samuelclay/turntouch-enclosure/inventor/STLs/Remote Assembly_Remote Top_1.stl

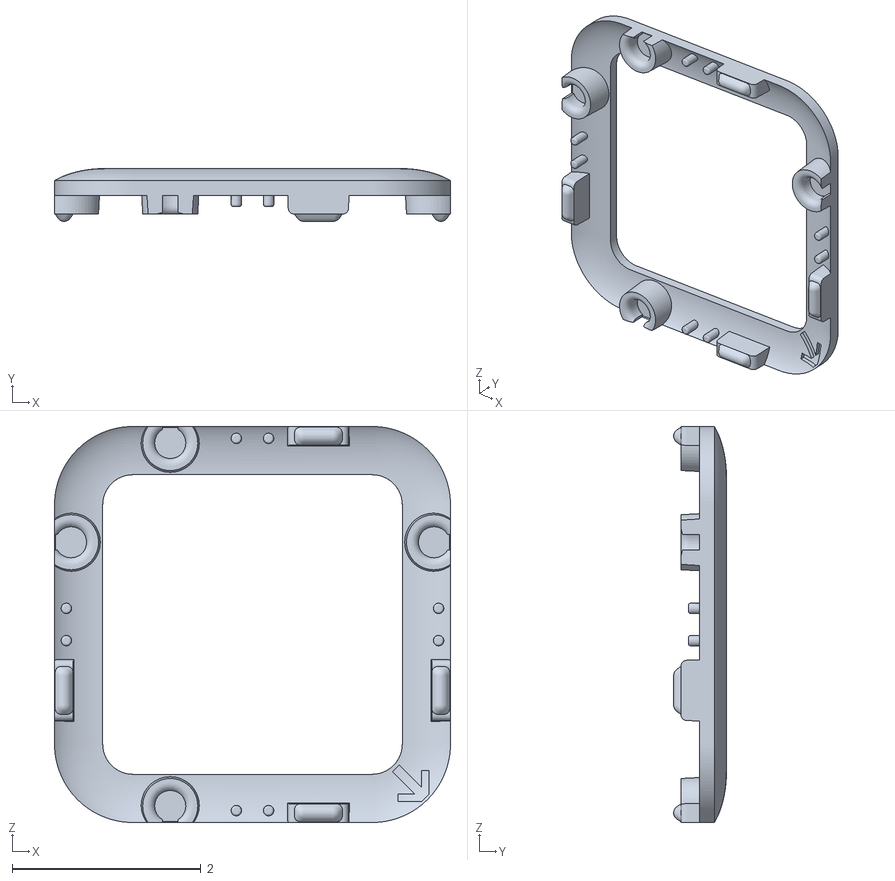
[picture p15: CAD file, 2016-02-05]
inventor/STLs/Remote Assembly_Remote Top_1.stl
4.20 x 0.56 x 4.20
