samuelclay/turntouch-enclosure/revisions/Turn Touch Remote Rev. 29/Remote Assembly_Eagle PCB rev 21_7.stl

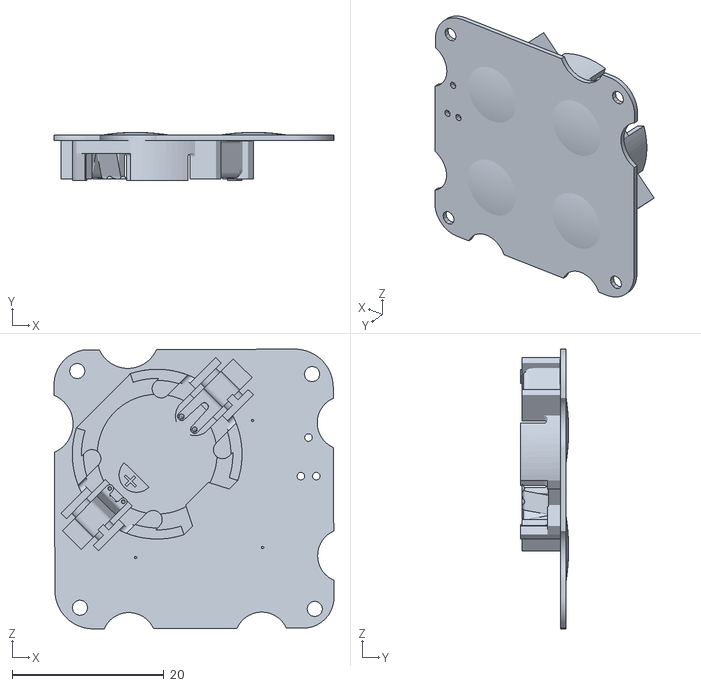
[picture p16: CAD file, 2015-10-15]
revisions/Turn Touch Remote Rev. 29/Remote Assembly_Eagle PCB rev 21_7.stl
37.0 x 6.37 x 36.9
