samuelclay/turntouch-enclosure/inventor/STLs/Remote Assembly_Remote Bottom_3.stl

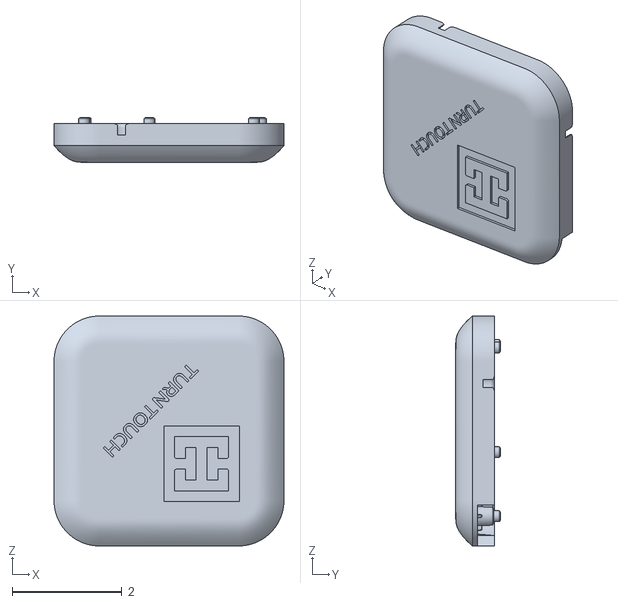
[picture p17: CAD file, 2016-02-05]
inventor/STLs/Remote Assembly_Remote Bottom_3.stl
4.20 x 0.813 x 4.20
