samuelclay/turntouch-enclosure/revisions/Turn Touch Remote Rev. 29/Remote Assembly_Remote Bottom_3.stl

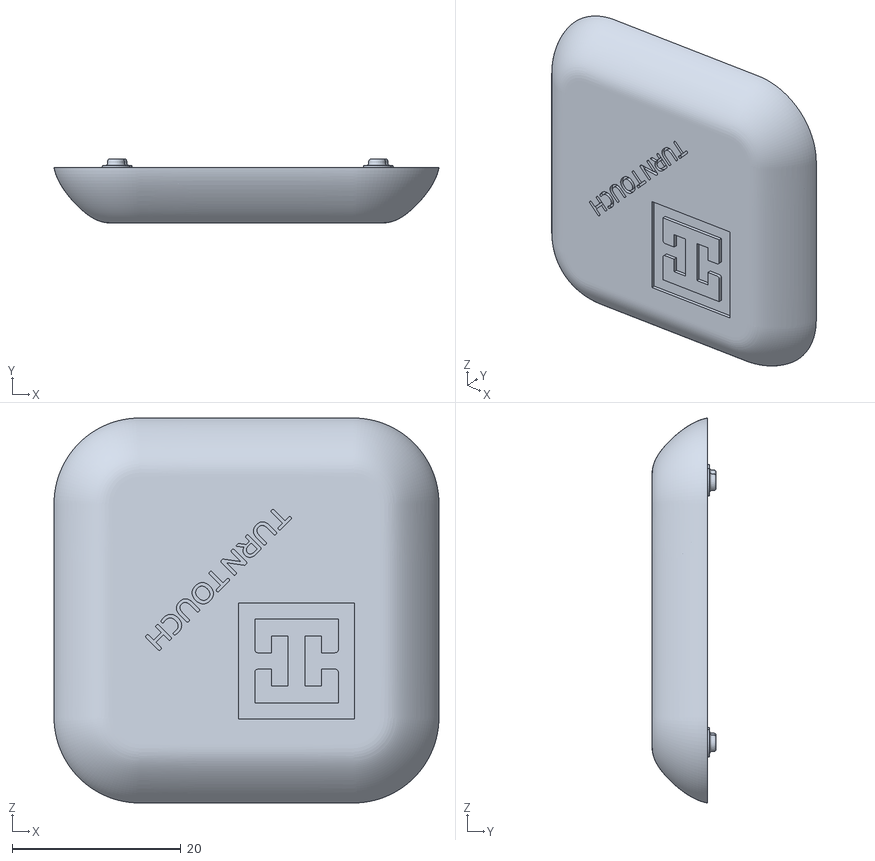
[picture p18: CAD file, 2015-10-15]
revisions/Turn Touch Remote Rev. 29/Remote Assembly_Remote Bottom_3.stl
45.7 x 7.62 x 45.7
