samuelclay/turntouch-enclosure/buttons.stl

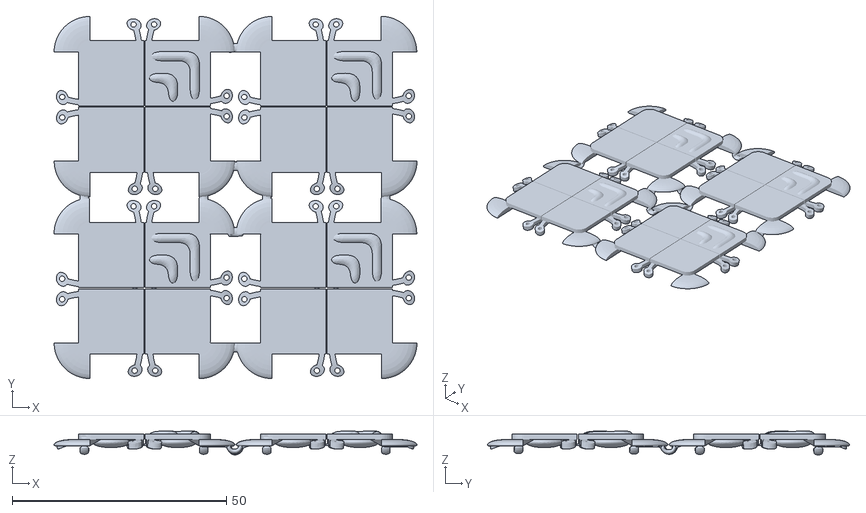
[picture p19: CAD file, 2015-05-16]
buttons.stl
84.7 x 84.5 x 5.56
