samuelclay/turntouch-enclosure/inventor/STLs/Magnet Top Insertion Jig.stl

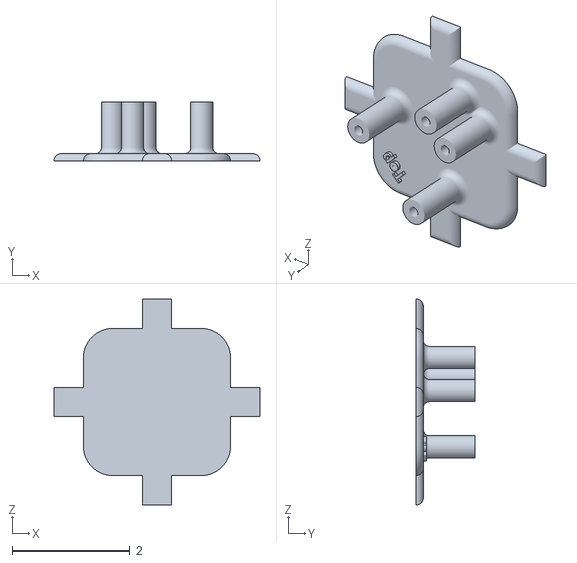
[picture p20: CAD file, 2017-12-07]
inventor/STLs/Magnet Top Insertion Jig.stl
3.50 x 1.00 x 3.50
