samuelclay/turntouch-enclosure/revisions/Turn Touch Remote IGES rev 29/Remote Buttons.igs

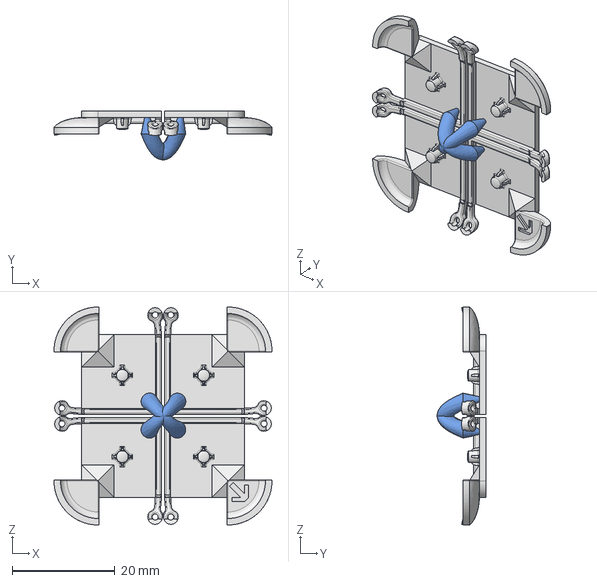
[picture p21: CAD file, 2015-10-19]
revisions/Turn Touch Remote IGES rev 29/Remote Buttons.igs
42.5 x 9.52 x 42.5 mm
