samuelclay/turntouch-enclosure/revisions/Turn Touch Remote rev 31/Plastic Remote Top.stp

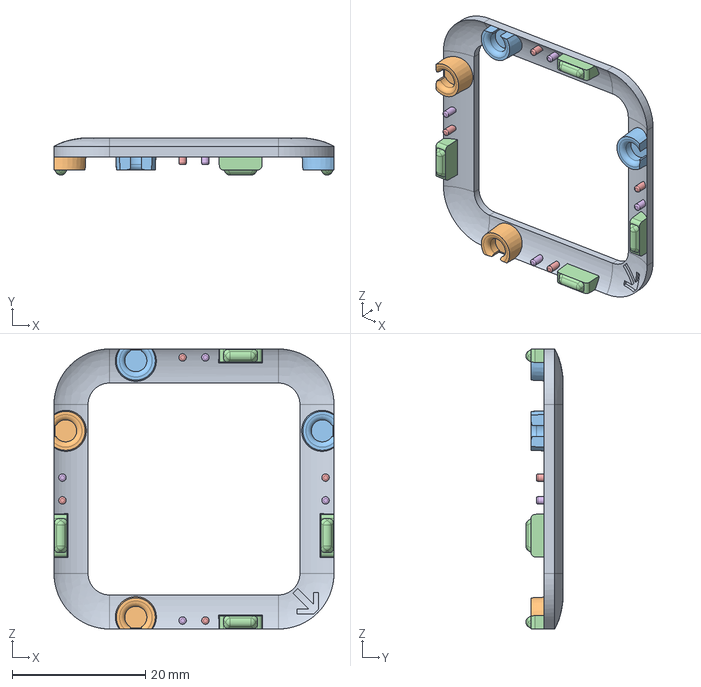
[picture p22: CAD file, 2016-02-05]
revisions/Turn Touch Remote rev 31/Plastic Remote Top.stp
42.0 x 5.60 x 42.0 mm
