samuelclay/turntouch-enclosure/revisions/Turn Touch rev 39/Remote Top.stp

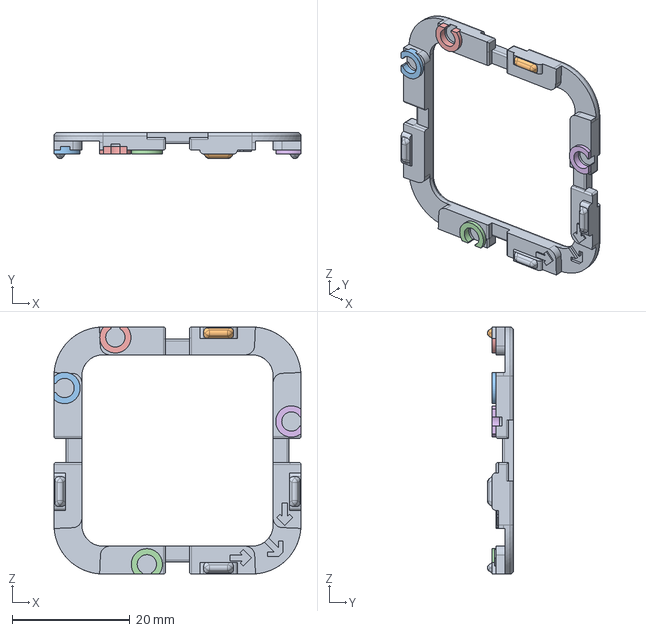
[picture p23: CAD file, 2017-05-08]
revisions/Turn Touch rev 39/Remote Top.stp
42.0 x 4.48 x 42.0 mm
