samuelclay/turntouch-enclosure/rhino/bottoms.stp

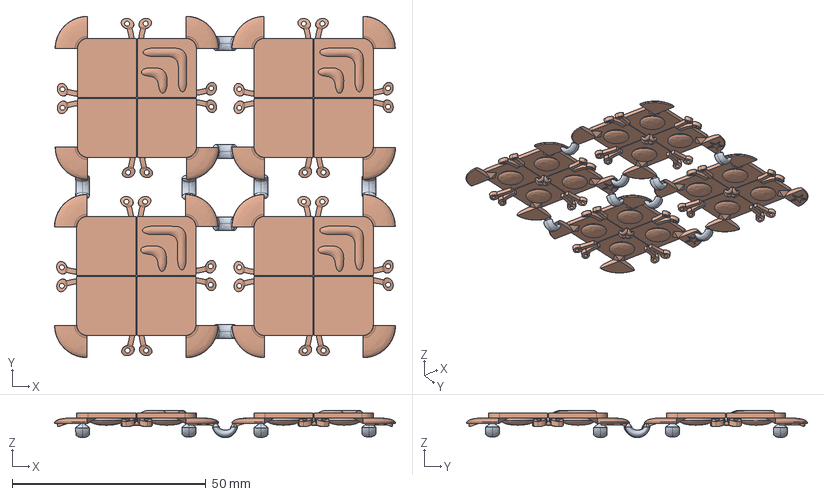
[picture p24: CAD file, 2015-06-04]
rhino/bottoms.stp
87.9 x 88.0 x 7.06 mm
