samuelclay/turntouch-enclosure/solidworks/Remote Buttons.SLDPRT

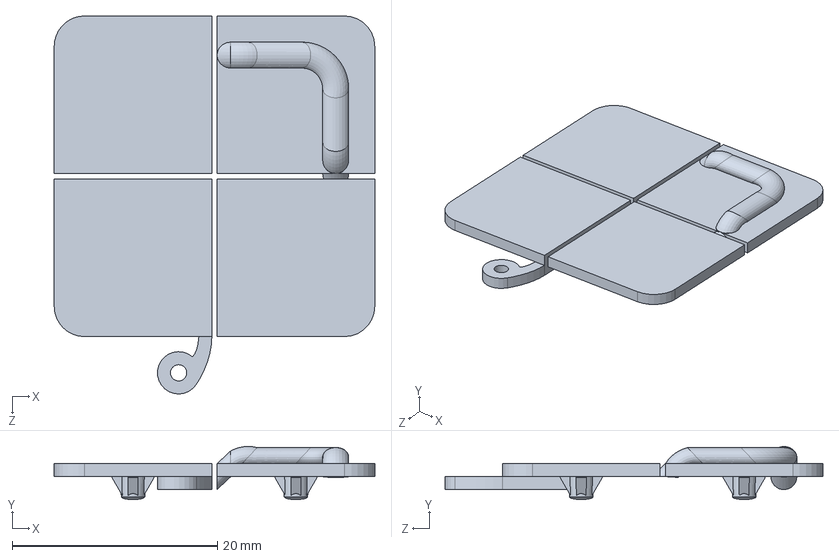
[picture p25: CAD file, 2015-06-16]
solidworks/Remote Buttons.SLDPRT
31.2 x 5.17 x 36.8 mm
