samuelclay/turntouch-enclosure/revisions/Turn Touch Remote IGES rev 29/Case Bottom.igs

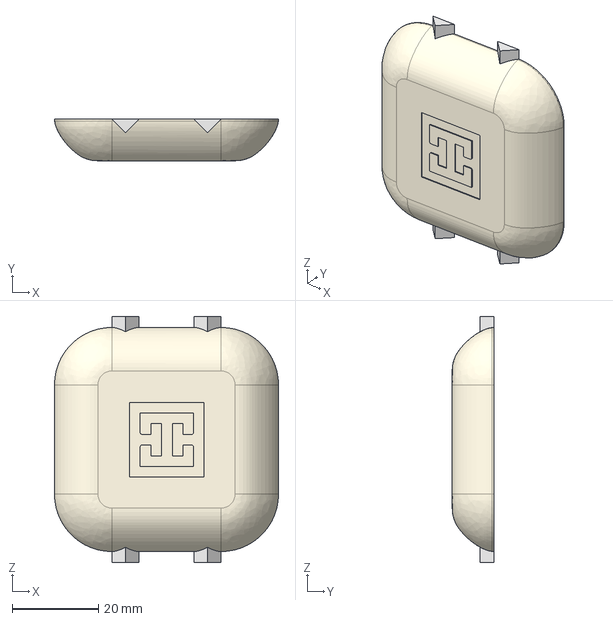
[picture p26: CAD file, 2015-10-19]
revisions/Turn Touch Remote IGES rev 29/Case Bottom.igs
51.9 x 9.63 x 57.0 mm
