samuelclay/turntouch-enclosure/revisions/Turn Touch rev 39/Remote Bottom.stp

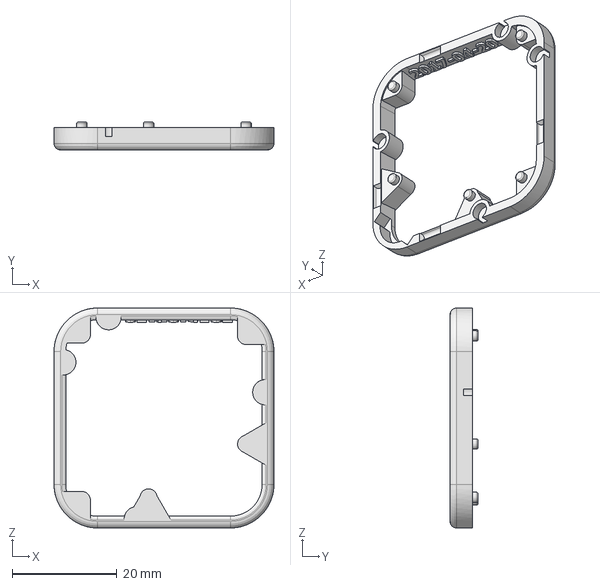
[picture p27: CAD file, 2017-05-08]
revisions/Turn Touch rev 39/Remote Bottom.stp
42.0 x 5.33 x 42.0 mm
