samuelclay/turntouch-enclosure/tops.stl

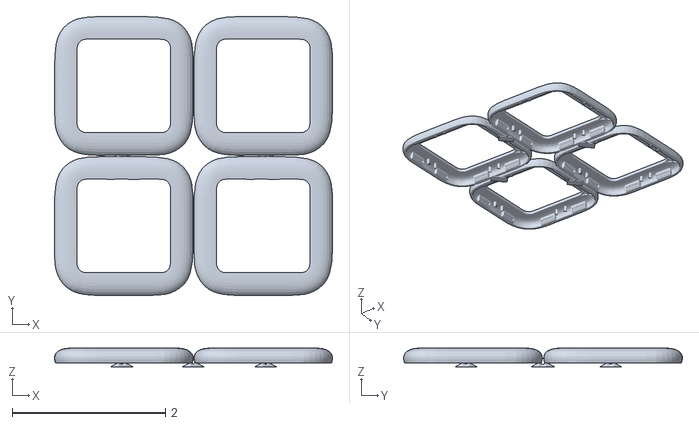
[picture p28: CAD file, 2015-05-07]
tops.stl
3.63 x 3.64 x 0.246
