samuelclay/turntouch-enclosure/bottoms.stl

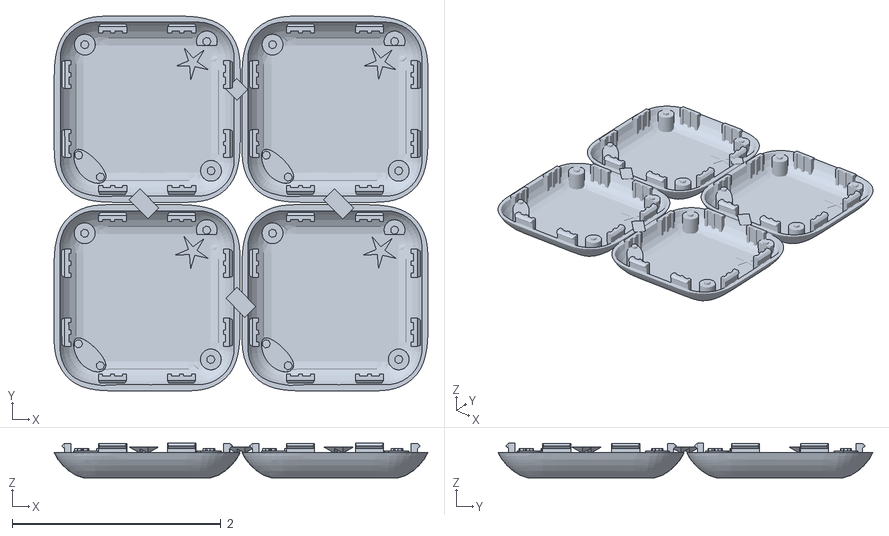
[picture p29: CAD file, 2015-05-07]
bottoms.stl
3.59 x 3.60 x 0.331
