samuelclay/turntouch-enclosure/inventor/STLs/Build Button Top Jig.stl

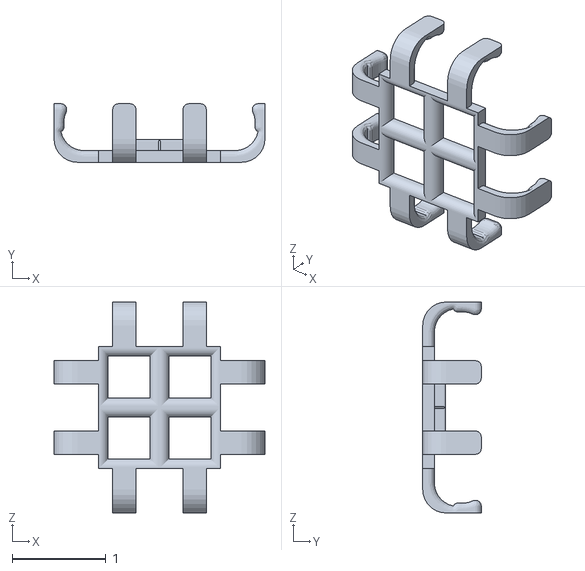
[picture p30: CAD file, 2017-12-01]
inventor/STLs/Build Button Top Jig.stl
2.25 x 0.625 x 2.25
