samuelclay/turntouch-enclosure/revisions/Turn Touch Remote IGES rev 29/Case Buttons.igs

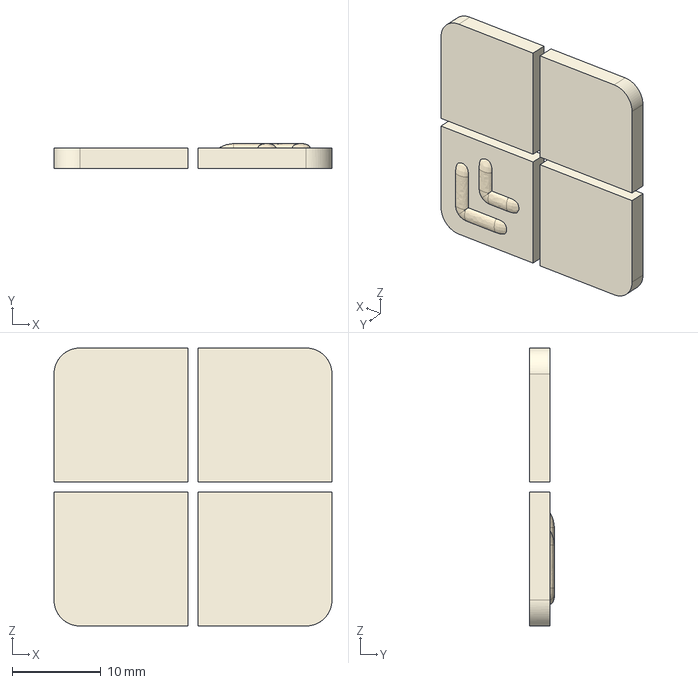
[picture p31: CAD file, 2015-10-19]
revisions/Turn Touch Remote IGES rev 29/Case Buttons.igs
31.2 x 2.79 x 31.2 mm
