samuelclay/turntouch-enclosure/revisions/Turn Touch Remote rev 31/Wood Case Bottom.stp

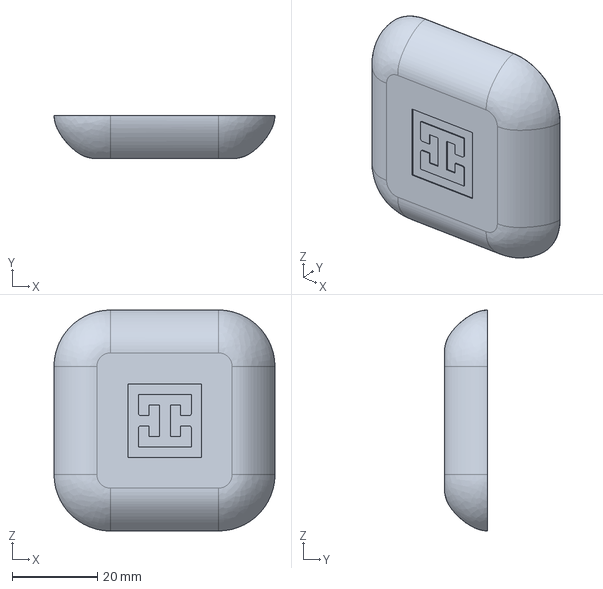
[picture p32: CAD file, 2016-02-05]
revisions/Turn Touch Remote rev 31/Wood Case Bottom.stp
51.9 x 10.2 x 51.9 mm
