samuelclay/turntouch-enclosure/revisions/Turn Touch rev 39/Remote Buttons.stp

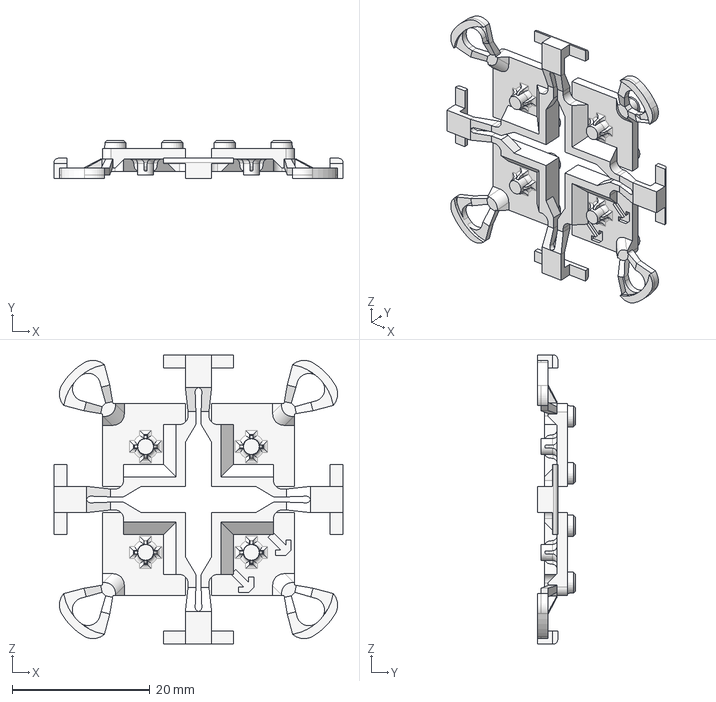
[picture p33: CAD file, 2017-05-08]
revisions/Turn Touch rev 39/Remote Buttons.stp
42.0 x 5.47 x 42.0 mm
