samuelclay/turntouch-enclosure/rhino/tops.stp

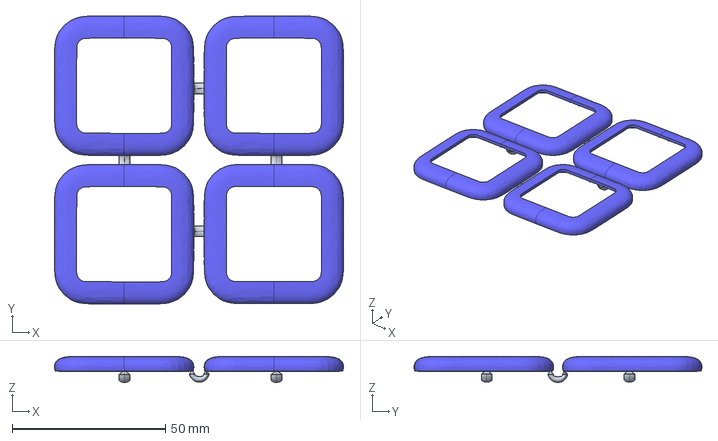
[picture p34: CAD file, 2015-05-22]
rhino/tops.stp
94.2 x 93.9 x 8.49 mm
