samuelclay/turntouch-enclosure/solidworks/Remote Top.sldprt

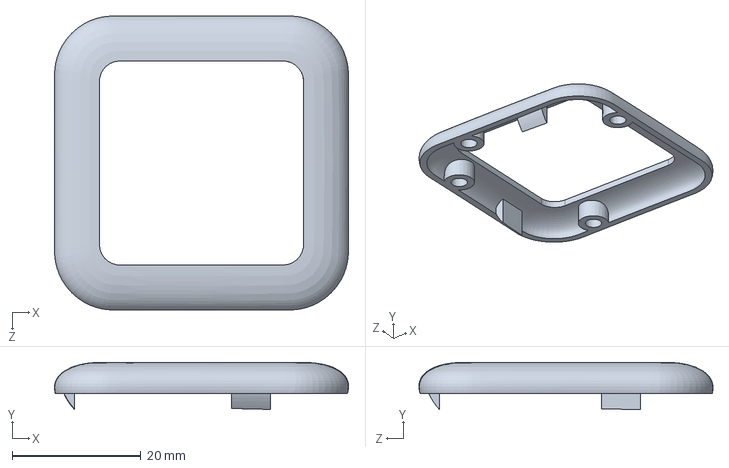
[picture p35: CAD file, 2015-06-13]
solidworks/Remote Top.sldprt
45.7 x 7.36 x 45.7 mm
