samuelclay/turntouch-enclosure/inventor/STEPs/Under Case Button Booster.stp

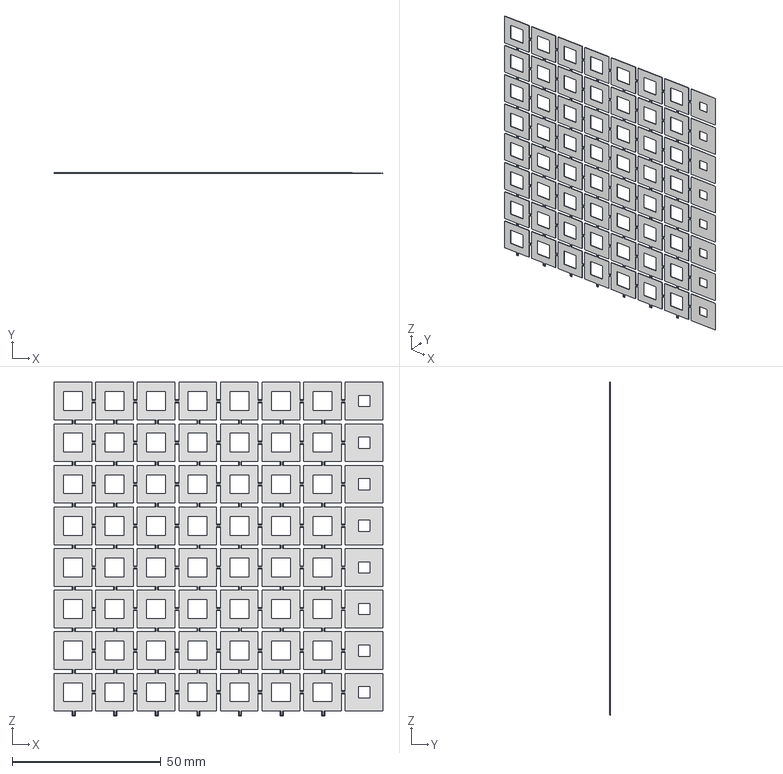
[picture p36: CAD file, 2016-10-12]
inventor/STEPs/Under Case Button Booster.stp
110.5 x 0.254 x 112.1 mm
