samuelclay/turntouch-enclosure/inventor/STLs/Under Case Photo Holder.stl

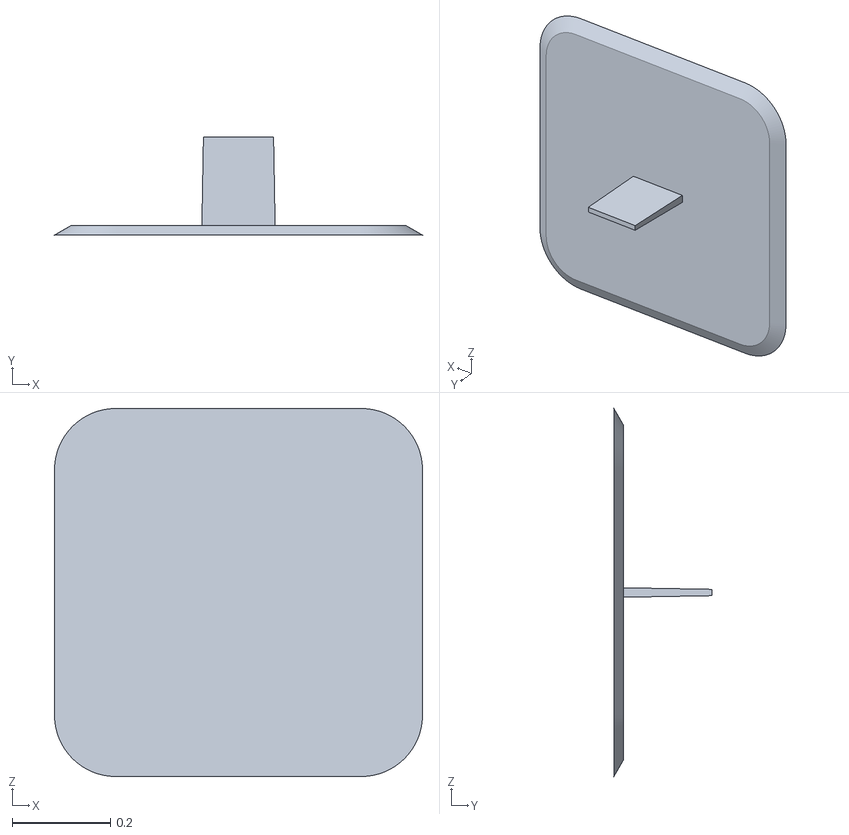
[picture p37: CAD file, 2017-01-26]
inventor/STLs/Under Case Photo Holder.stl
0.75 x 0.2 x 0.75
