samuelclay/turntouch-enclosure/Remote enclosure.obj

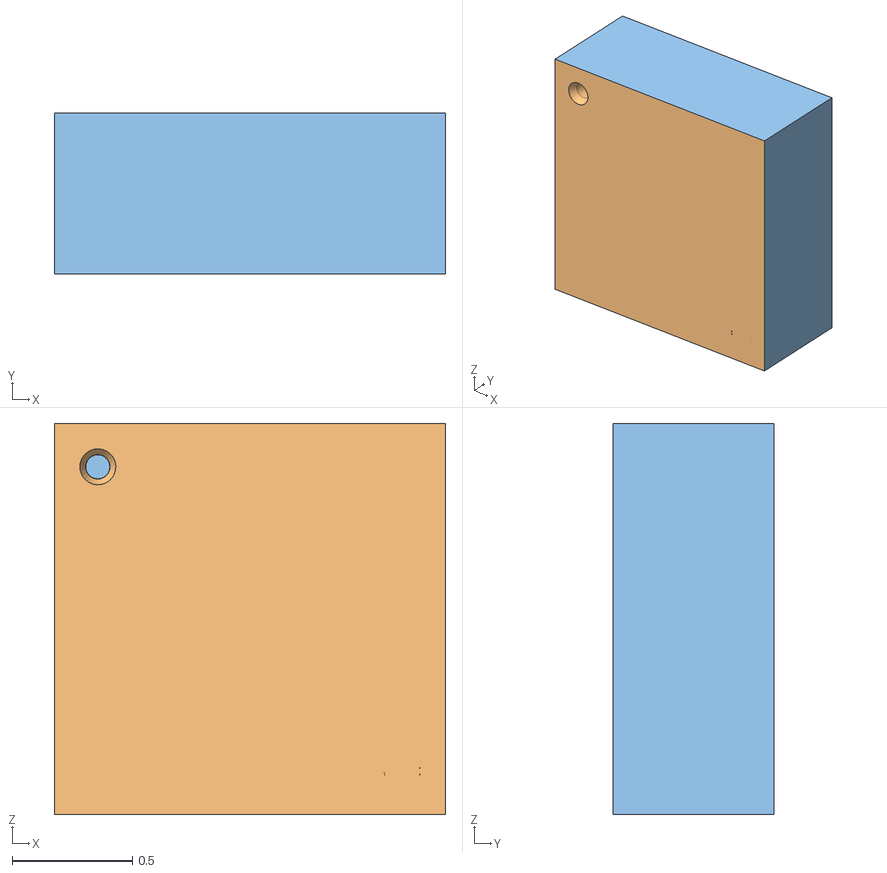
[picture p38: CAD file, 2014-10-08]
Remote enclosure.obj
1.63 x 0.67 x 1.62
Mesh1 PCB Model
Mesh91 Bottom___05__walls_ Model
Mesh102 Top___05__walls_ Model
Mesh116 Button_cap1 Model
Mesh120 Button_cap2 Model
Mesh124 Button_cap3 Model
Mesh128 Button_cap4 Model
