samuelclay/turntouch-enclosure/revisions/Turn Touch Remote rev 31/Wood Case Top.stp

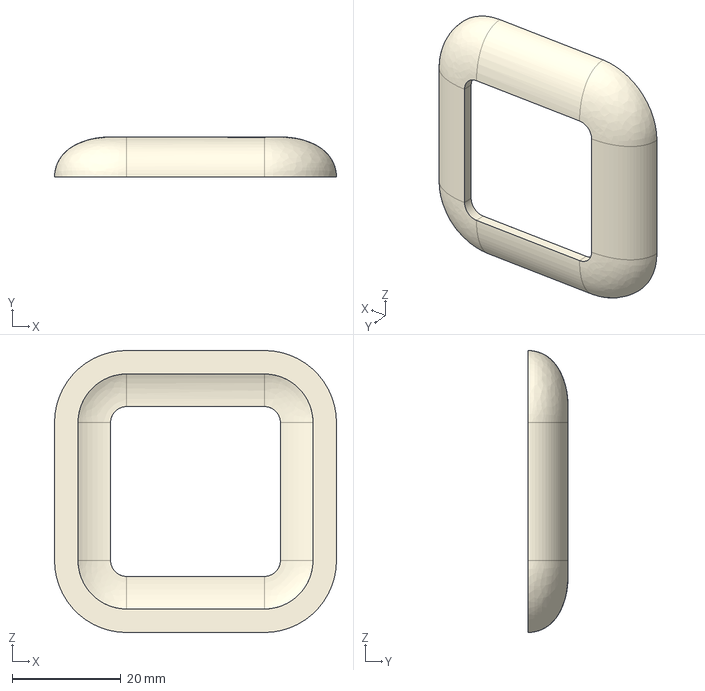
[picture p39: CAD file, 2016-02-05]
revisions/Turn Touch Remote rev 31/Wood Case Top.stp
51.9 x 7.37 x 51.9 mm
