samuelclay/turntouch-enclosure/rhino/remote.stp

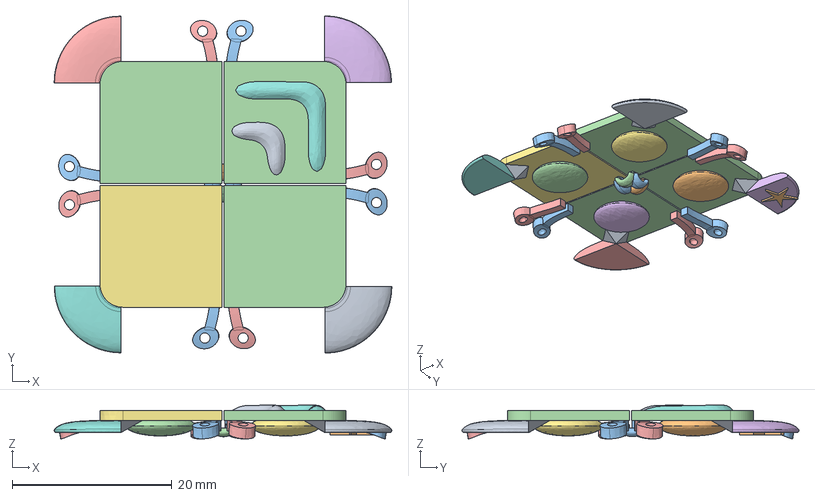
[picture p40: CAD file, 2015-05-19]
rhino/remote.stp
42.2 x 42.1 x 4.23 mm
