samuelclay/turntouch-enclosure/solidworks/PCB.SLDPRT

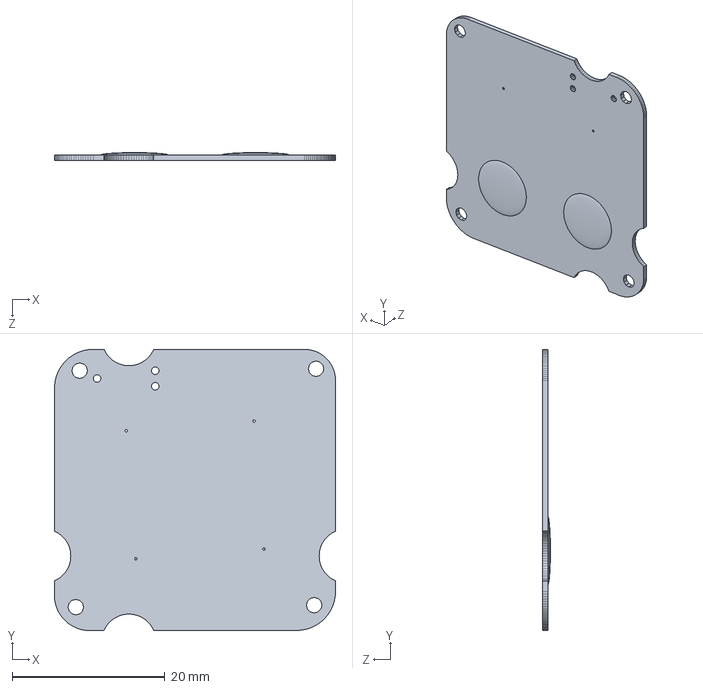
[picture p41: CAD file, 2015-06-09]
solidworks/PCB.SLDPRT
36.8 x 36.9 x 1.03 mm
