samuelclay/turntouch-enclosure/inventor/Eagle PCB rev 38.dxf

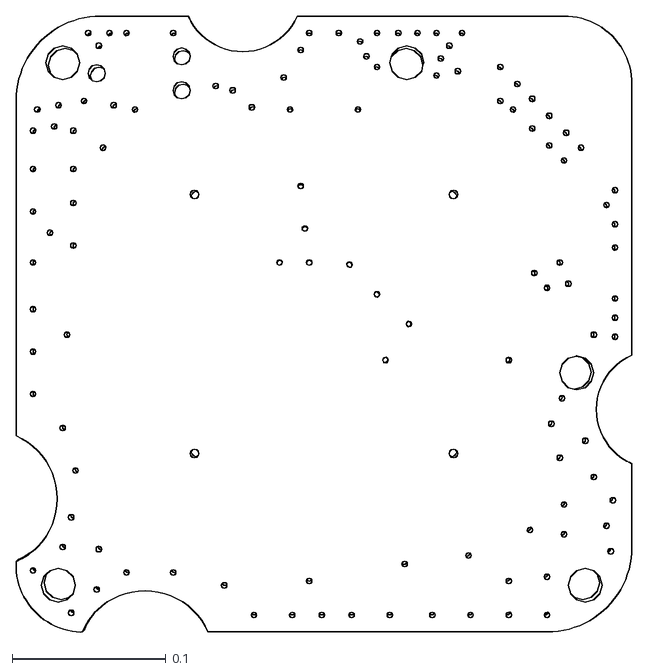
[picture p42: CAD file, 2017-04-11]
inventor/Eagle PCB rev 38.dxf
0.4 x 0.4
