samuelclay/turntouch-enclosure/revisions/Turn Touch Remote rev 31/Plastic Remote Bottom.stp

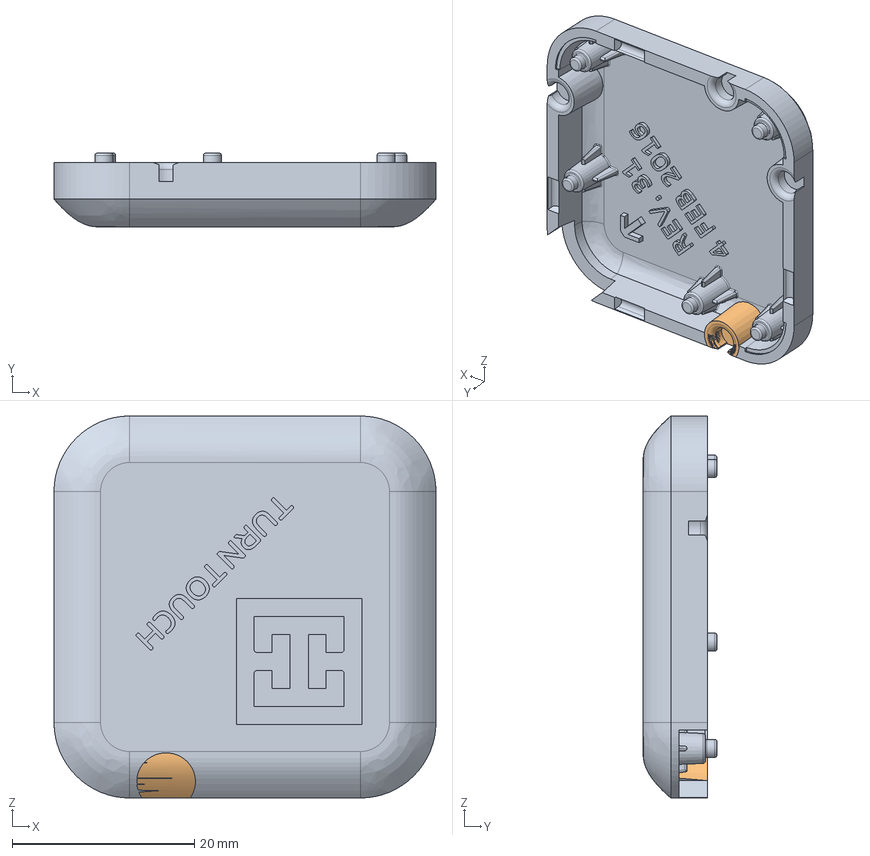
[picture p43: CAD file, 2016-02-05]
revisions/Turn Touch Remote rev 31/Plastic Remote Bottom.stp
42.0 x 8.13 x 42.0 mm
