samuelclay/turntouch-enclosure/solidworks/Remote Bottom.sldprt

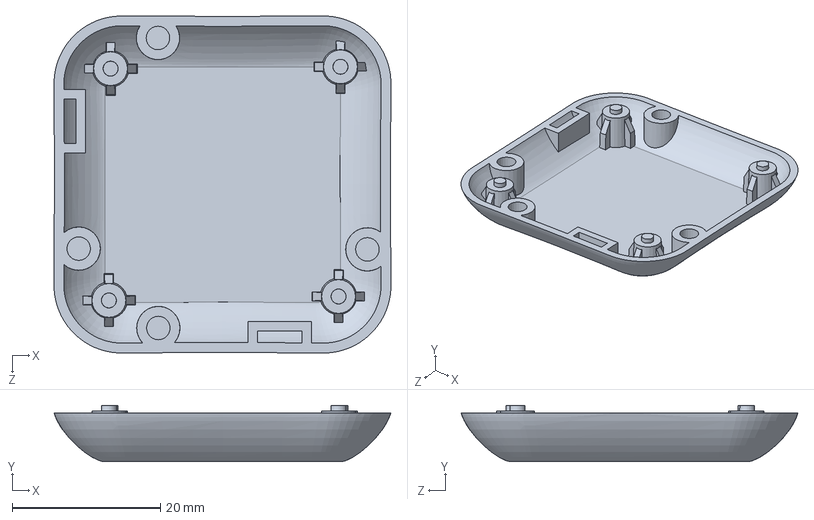
[picture p44: CAD file, 2015-06-07]
solidworks/Remote Bottom.sldprt
45.5 x 7.62 x 45.5 mm
