samuelclay/turntouch-enclosure/revisions/Turn Touch Remote IGES rev 29/Case Top.igs

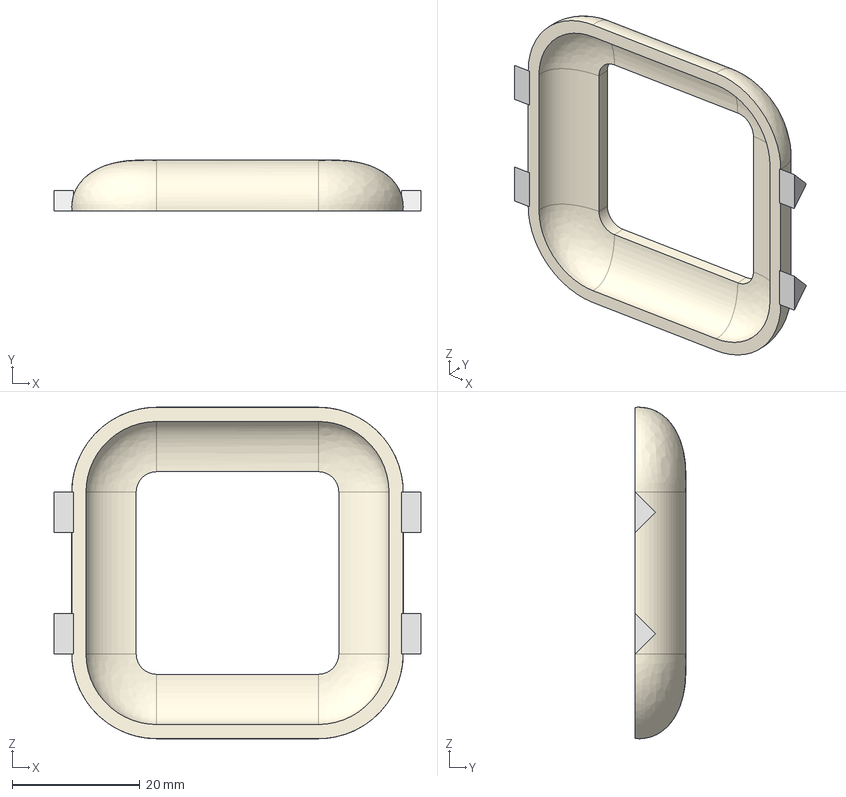
[picture p45: CAD file, 2015-10-19]
revisions/Turn Touch Remote IGES rev 29/Case Top.igs
57.5 x 7.92 x 52.0 mm
