samuelclay/turntouch-enclosure/revisions/Turn Touch Remote rev 31/Wood Case Buttons.stp

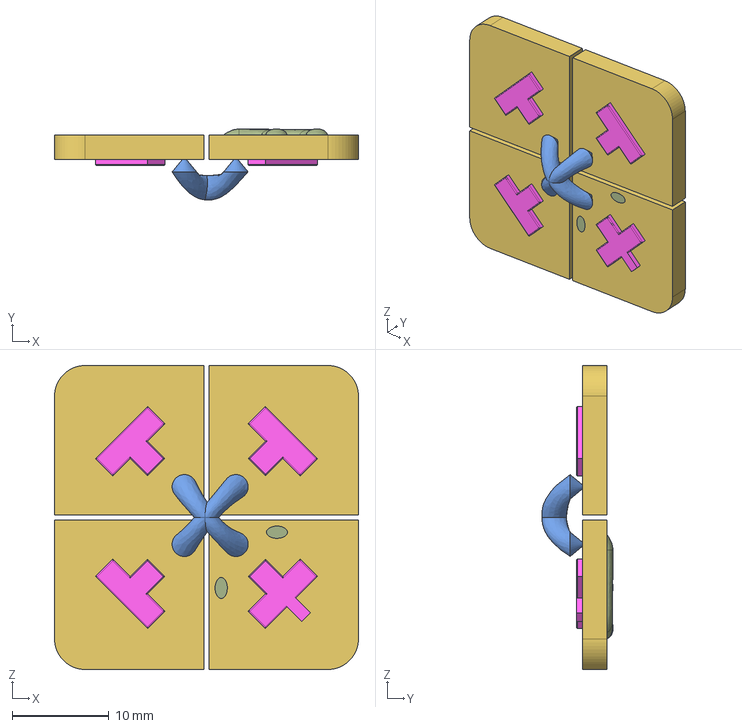
[picture p46: CAD file, 2015-08-21]
revisions/Turn Touch Remote rev 31/Wood Case Buttons.stp
31.5 x 7.37 x 31.5 mm
