samuelclay/turntouch-enclosure/rhino/top.stp

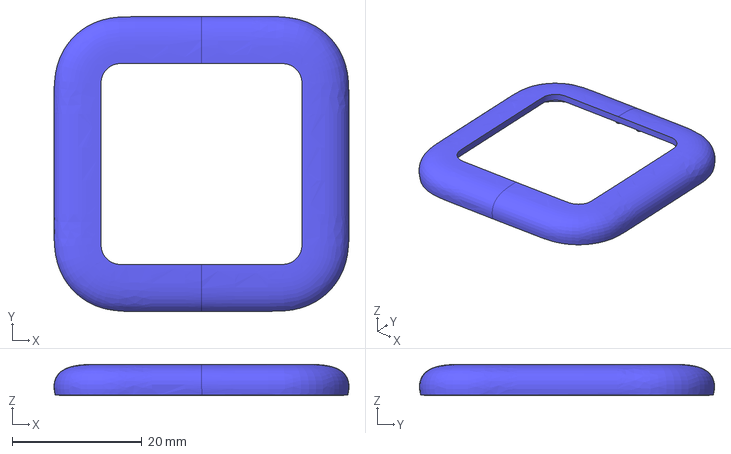
[picture p47: CAD file, 2015-05-19]
rhino/top.stp
45.4 x 45.4 x 4.84 mm
