samuelclay/turntouch-enclosure/solidworks/Remote Shell.SLDPRT

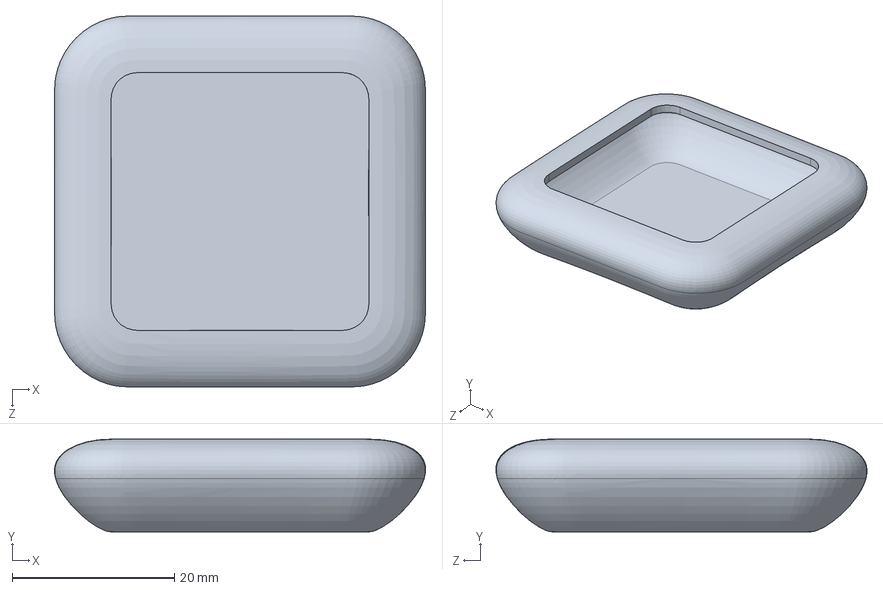
[picture p48: CAD file, 2015-06-06]
solidworks/Remote Shell.SLDPRT
45.7 x 11.4 x 45.7 mm
