samuelclay/turntouch-enclosure/revisions/Turn Touch Remote IGES rev 29/Remote Top.igs

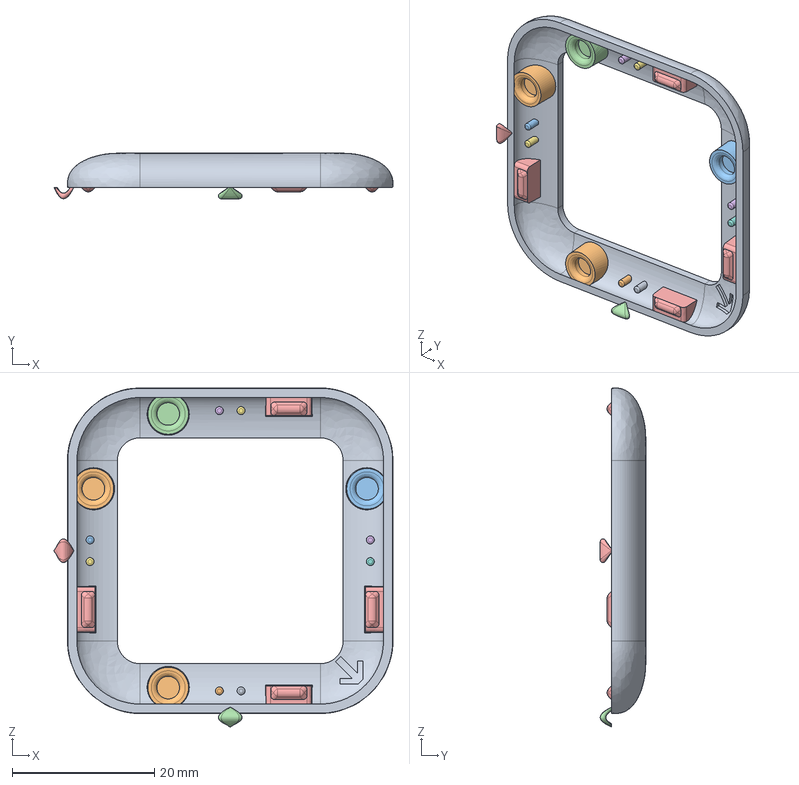
[picture p49: CAD file, 2015-10-19]
revisions/Turn Touch Remote IGES rev 29/Remote Top.igs
47.7 x 6.42 x 47.7 mm
