samuelclay/turntouch-enclosure/rhino/bottom.stp

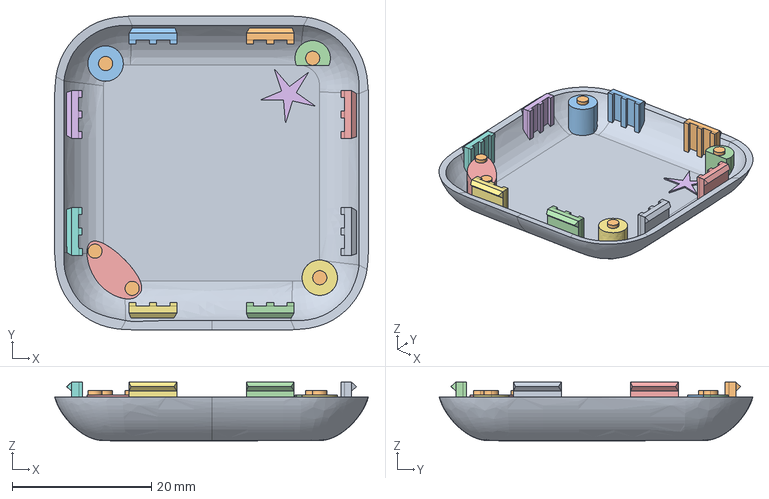
[picture p50: CAD file, 2015-05-19]
rhino/bottom.stp
45.1 x 45.1 x 8.46 mm
