samuelclay/turntouch-enclosure/inventor/STLs/Case Button Jig.stl

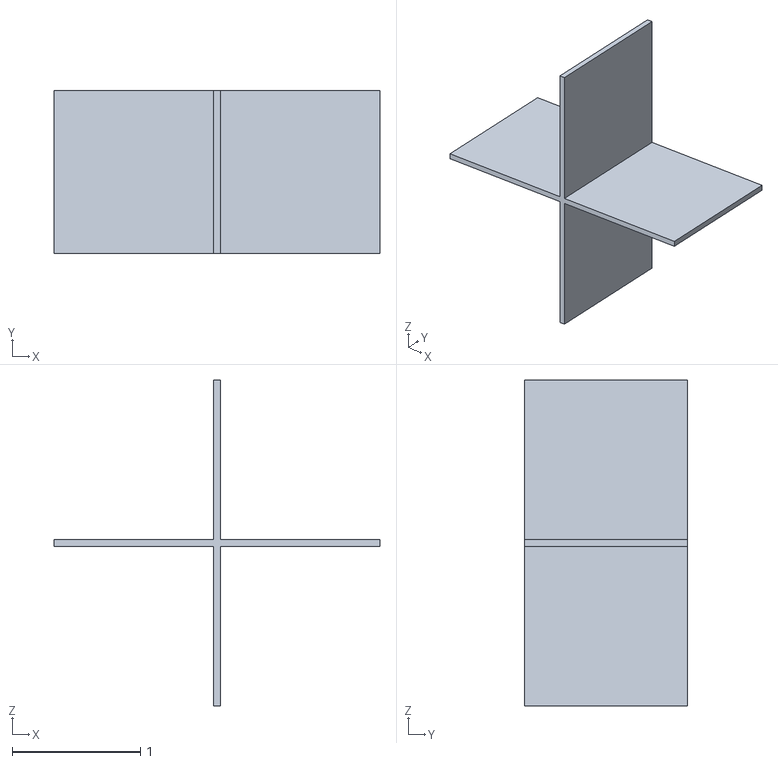
[picture p51: CAD file, 2016-01-06]
inventor/STLs/Case Button Jig.stl
2.54 x 1.27 x 2.54
