samuelclay/turntouch-enclosure/inventor/cr2032B Metal Battery Holder.SLDPRT

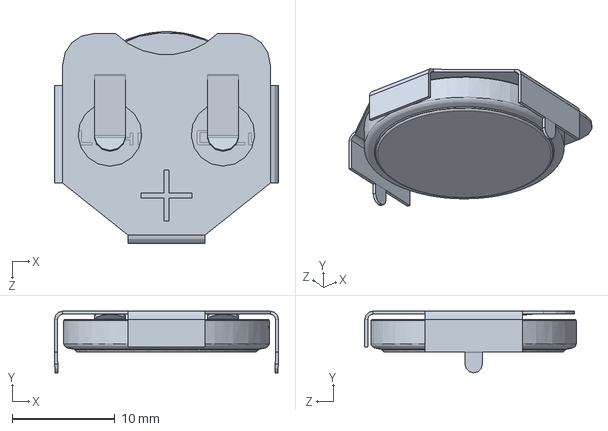
[picture p52: CAD file, 2017-03-19]
inventor/cr2032B Metal Battery Holder.SLDPRT
21.8 x 6.01 x 20.6 mm
