samuelclay/turntouch-enclosure/inventor/CR2032 Battery Holder.stp

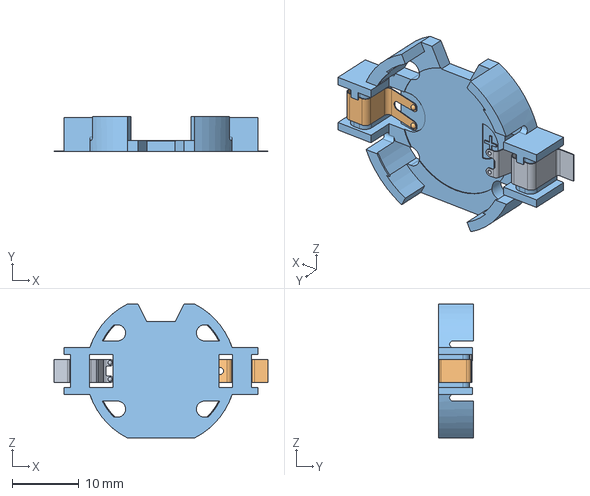
[picture p53: CAD file, 2015-08-21]
inventor/CR2032 Battery Holder.stp
32.0 x 5.30 x 20.0 mm
