samuelclay/turntouch-enclosure/revisions/Turn Touch rev 37/Remote Buttons.pdf

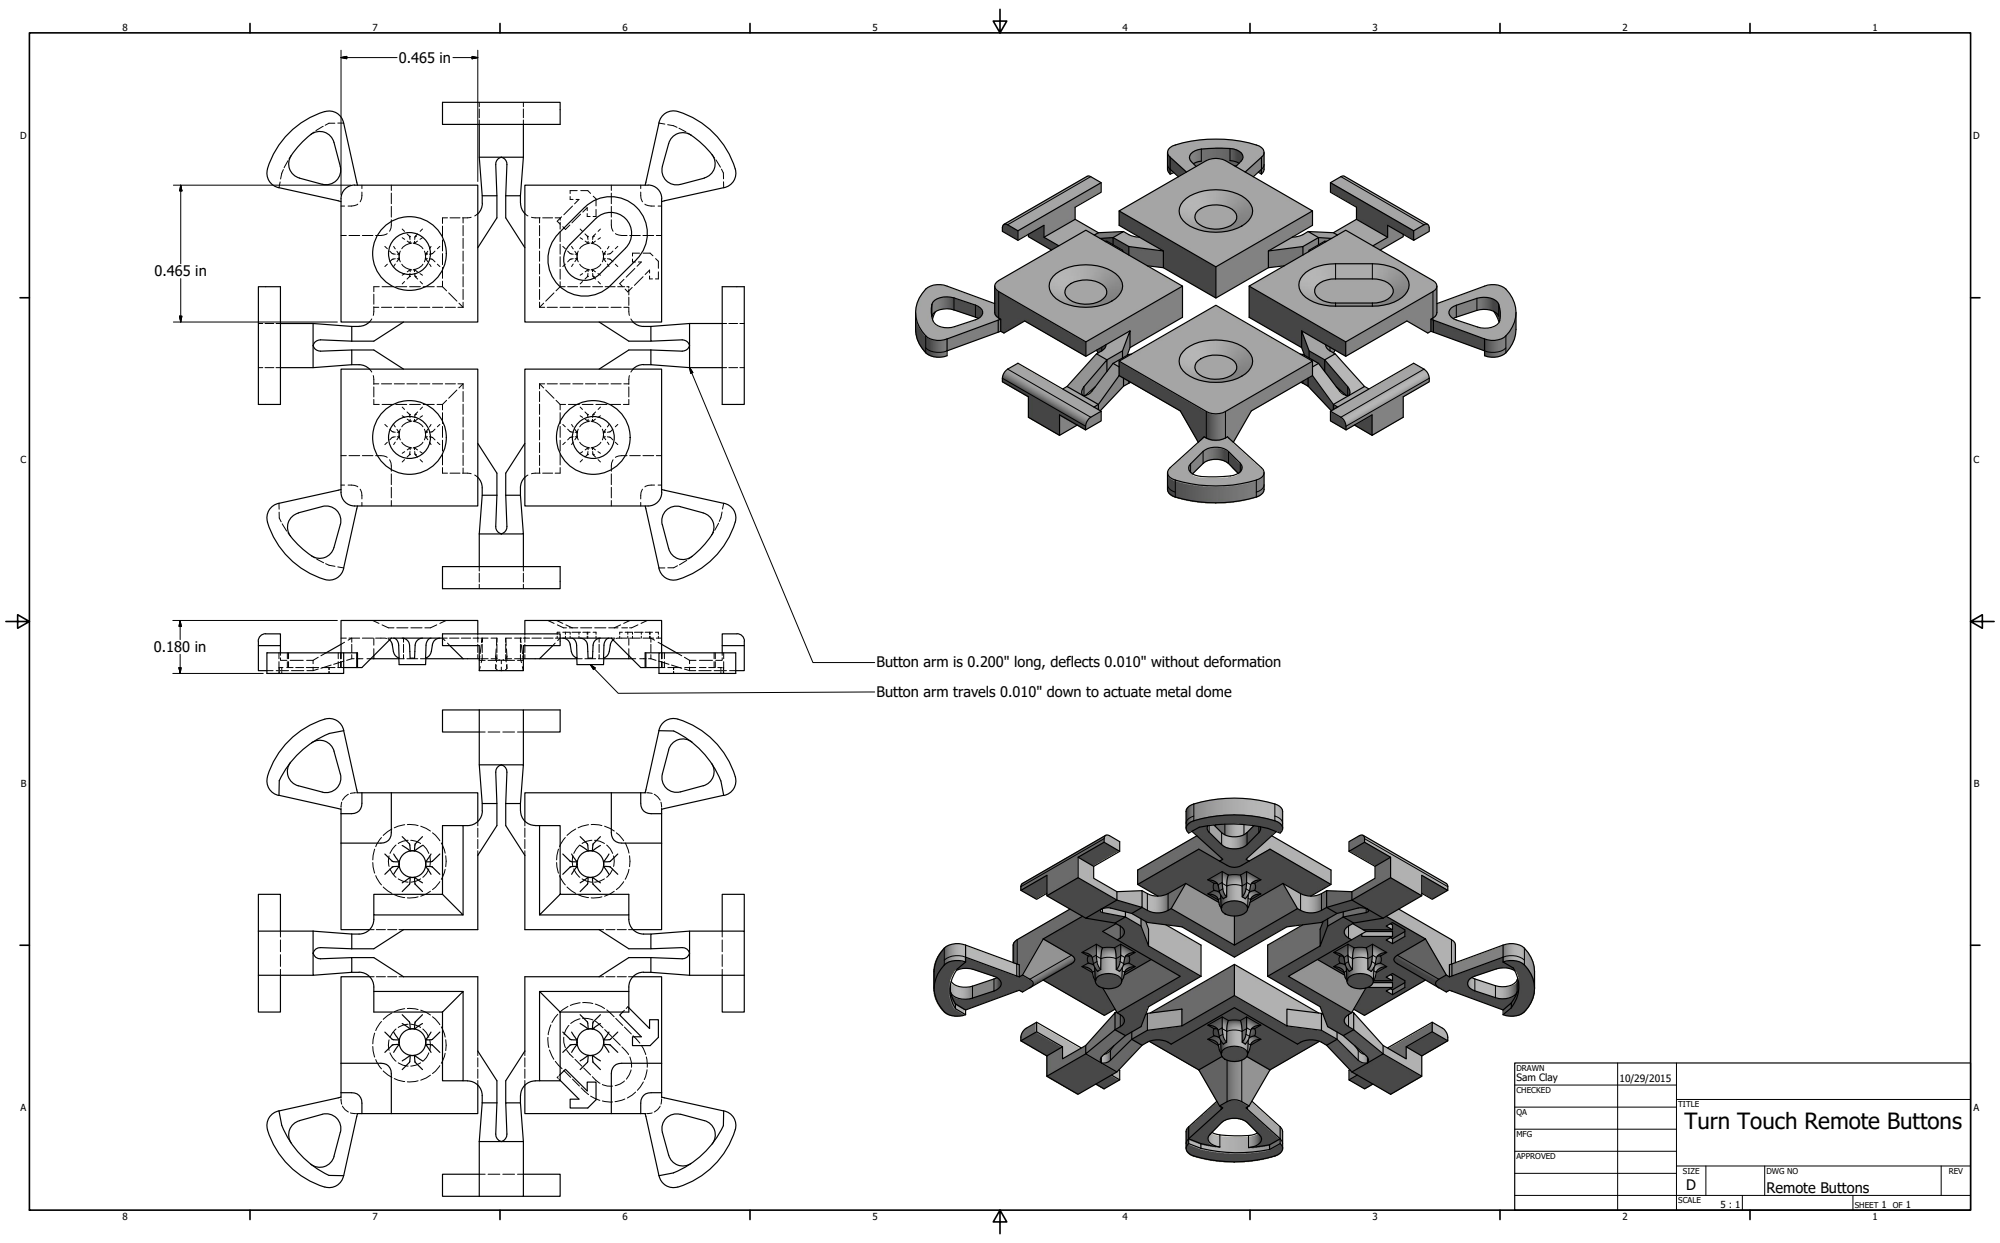
[picture p62: page 1]
SHEET 1 OF 1; DRAWN; CHECKED; MFG; APPROVED; Sam Clay; DWG NO Remote Buttons; SIZE D; SCALE; REV

Button arm is 0.200" long, deflects 0.010" without deformation

Button arm travels 0.010" down to actuate metal dome

TITLE
Turn Touch Remote Buttons
