samuelclay/turntouch-enclosure/revisions/Turn Touch rev 37/Remote Top.pdf

1.652 in

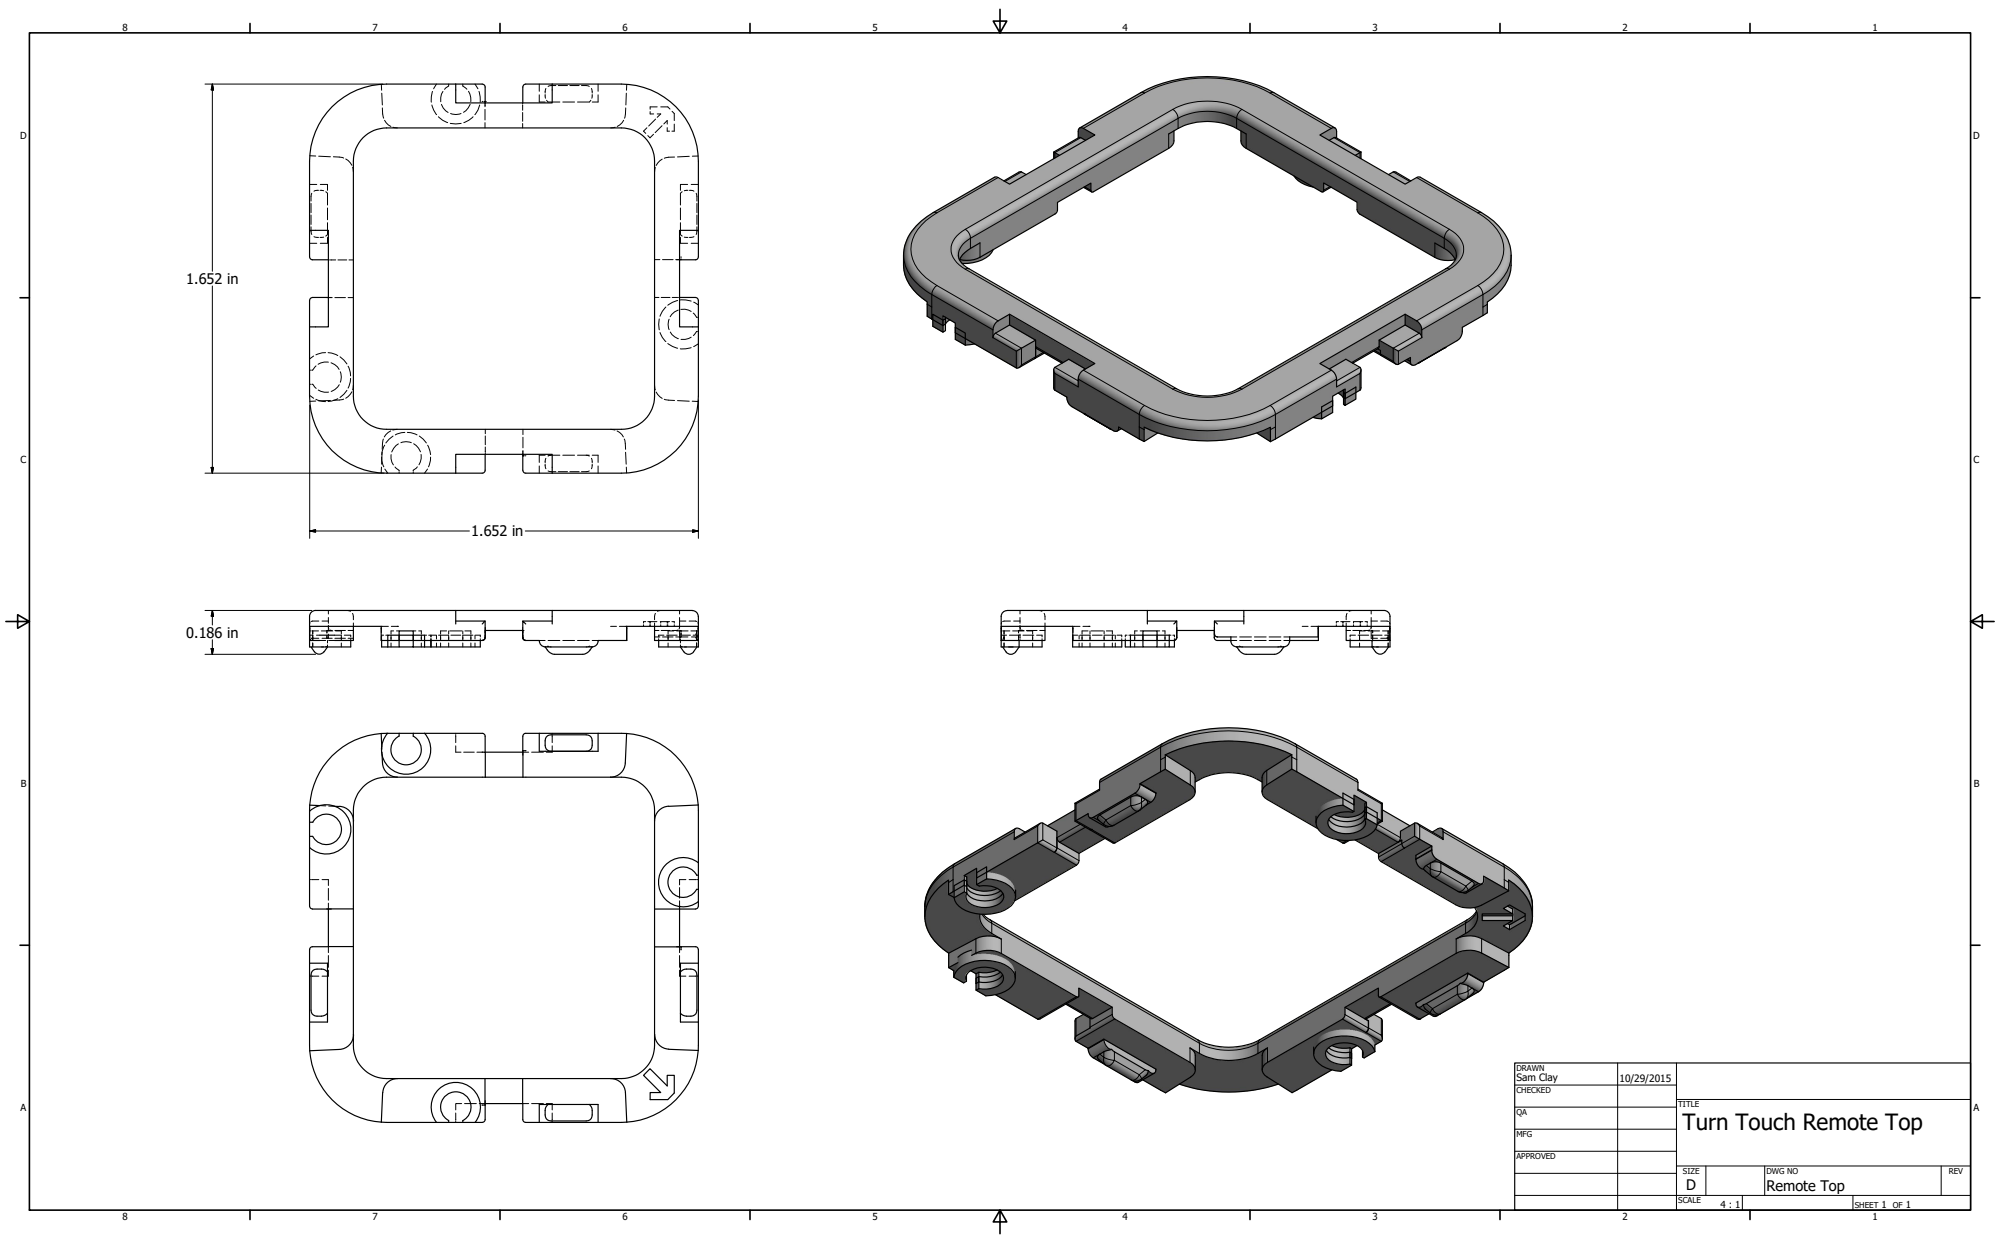
[picture p63: page 1]
SHEET 1 OF 1; DRAWN; CHECKED; MFG; APPROVED; Sam Clay; DWG NO Remote Top; SIZE D; SCALE; REV

TITLE
Turn Touch Remote Top
